sherrardTr4129/Wireless-Modular-Haptic-Controller/ros_software/haptic_orientation_capture_driver/src/SerialManagerClass.py

#!/usr/bin/python

# Author: Trevor Sherrad
# Course: Directed Research
# Since: Feburary 3rd, 2020
#
# Description: This file defines the class that will be used to manage
#              the serial connection between the arduino nano reciever and 
#              the rest of the ROS system

import serial

class SerialManager:
    def __init__(self, port, baud):
        self.port = port
        self.baud = baud
        self.serObj = None

    def open(self):
        # construct serial object
        serObj = serial.Serial()

        # set individual object fields
        serObj.port = self.port
        serObj.baudrate = self.baud
        serObj.byteSize = serial.EIGHTBITS
        serObj.parity = serial.PARITY_NONE
        serObj.stopbits = serial.STOPBITS_ONE

        # attempt to open port
        try:
            serObj.open()
        except Exception, err:
            print("error opening serial port: %s" % err)

        # check if serial is open
        res = serObj.isOpen()

        if(res):
            self.serObj = serObj
            return res
        else:
            self.serObj = None
            return res

    def read(self):
        # try to read from the serial object
        line = self.serObj.readline()
        return line

    def write(self, stringToWrite):
        # attempt to write string as 
        # bytes to serial port

        # format string
        bytesToWrite = stringToWrite.encode('utf-8')

        # write to serial port
        self.serObj.write(bytesToWrite)


    def close(self):
        # close the serial port
        self.serObj.close()
